fishros/fishbot-motion-control/docs/esp-drone/docs/_static/AFS_SEL.png

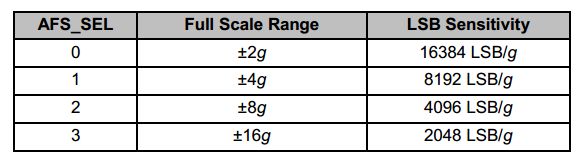
docs/esp-drone/docs/_static/AFS_SEL.png
