fishros/fishbot-motion-control/docs/esp-drone/docs/_static/api-reference.png

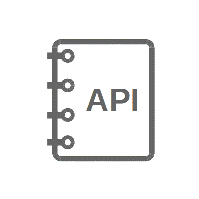
docs/esp-drone/docs/_static/api-reference.png
