fishros/fishbot-motion-control/docs/esp-drone/docs/_static/burst_read_sequence.png

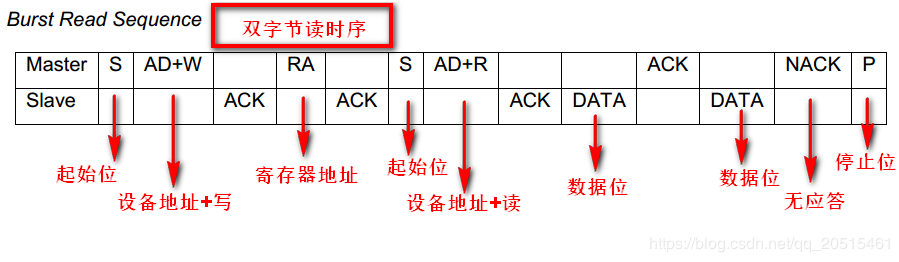
docs/esp-drone/docs/_static/burst_read_sequence.png
