fishros/fishbot-motion-control/docs/esp-drone/docs/_static/burst_write_sequence.png

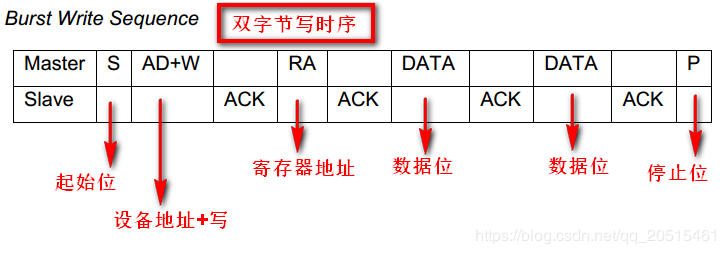
docs/esp-drone/docs/_static/burst_write_sequence.png
