fishros/fishbot-motion-control/docs/esp-drone/docs/_static/cover_page_pdf.jpg

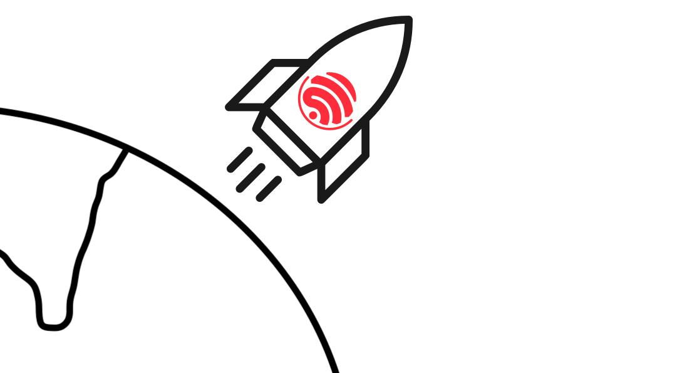
docs/esp-drone/docs/_static/cover_page_pdf.jpg
