fishros/fishbot-motion-control/docs/esp-drone/docs/_static/drivers_flie_struture.png

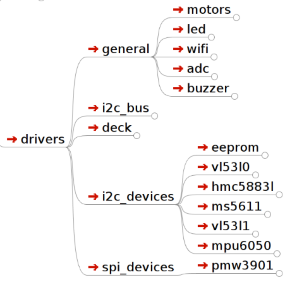
docs/esp-drone/docs/_static/drivers_flie_struture.png
