fishros/fishbot-motion-control/docs/esp-drone/docs/_static/espdrone_file_structure.png

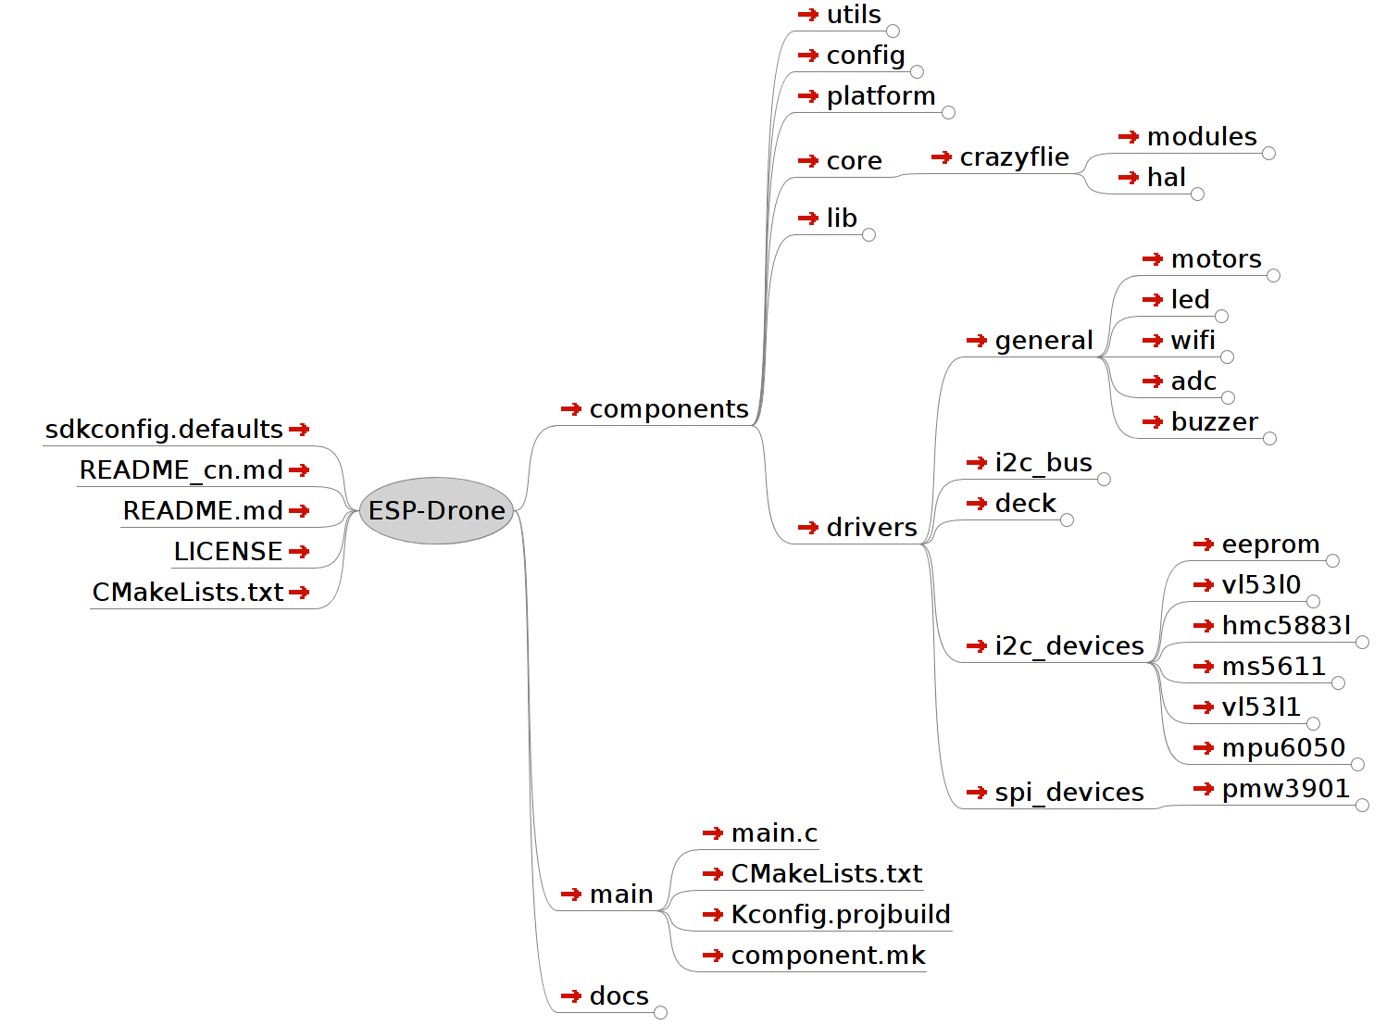
docs/esp-drone/docs/_static/espdrone_file_structure.png
