fishros/fishbot-motion-control/docs/esp-drone/docs/_static/espdrone_s2_v1_2_up2.jpg

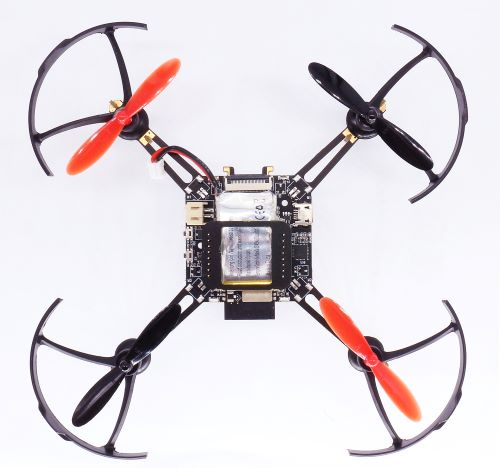
docs/esp-drone/docs/_static/espdrone_s2_v1_2_up2.jpg
