fishros/fishbot-motion-control/docs/esp-drone/docs/_static/espilot_app.png

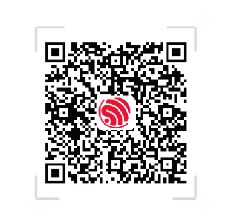
docs/esp-drone/docs/_static/espilot_app.png
