fishros/fishbot-motion-control/docs/esp-drone/docs/_static/esplane_2_0.jpg

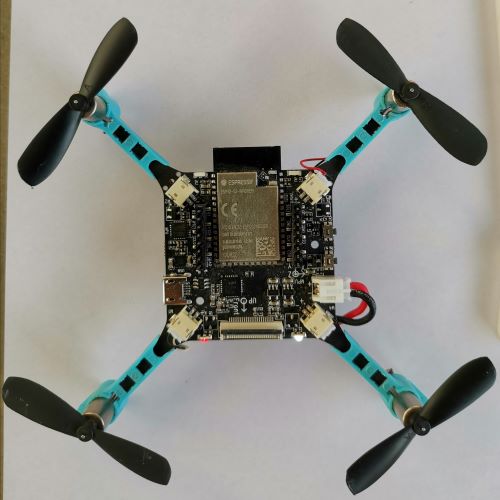
docs/esp-drone/docs/_static/esplane_2_0.jpg
