fishros/fishbot-motion-control/docs/esp-drone/docs/_static/FS_SEL.png

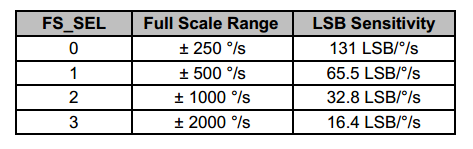
docs/esp-drone/docs/_static/FS_SEL.png
