fishros/fishbot-motion-control/docs/esp-drone/docs/_static/gamepad.jpg

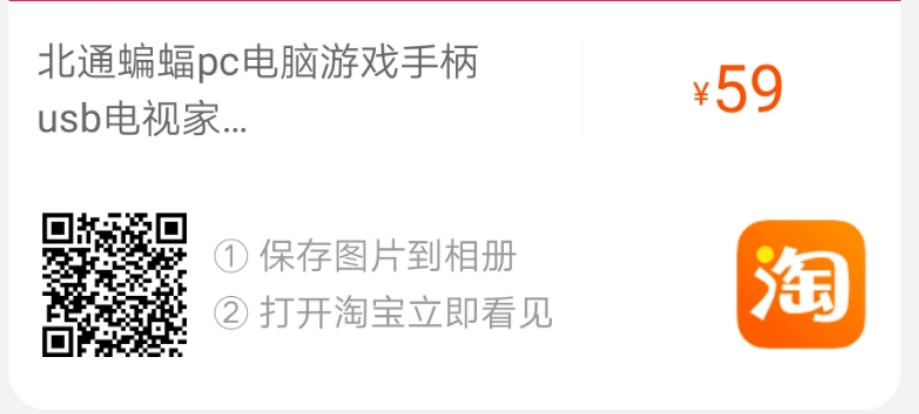
docs/esp-drone/docs/_static/gamepad.jpg
