fishros/fishbot-motion-control/docs/esp-drone/docs/_static/General-framework-of-the-stabilization-structure-of-the-crazyflie-with-setpoint-handling.png

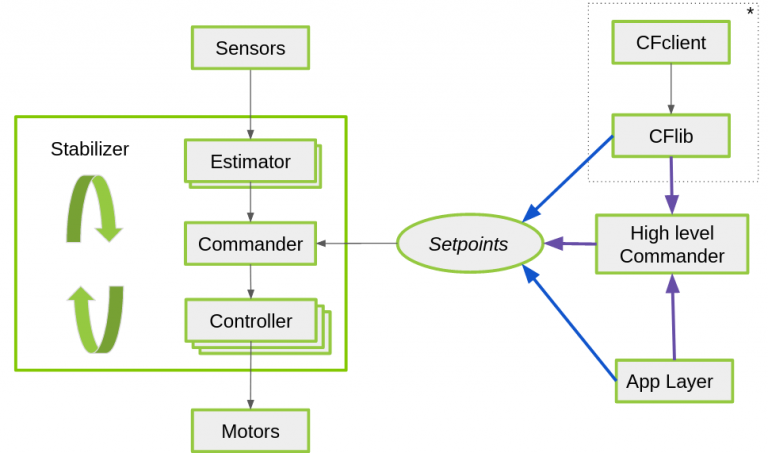
docs/esp-drone/docs/_static/General-framework-of-the-stabilization-structure-of-the-crazyflie-with-setpoint-handling.png
