fishros/fishbot-motion-control/docs/esp-drone/docs/_static/get-started.png

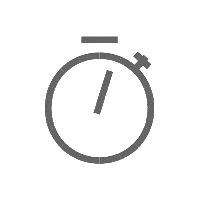
docs/esp-drone/docs/_static/get-started.png
