fishros/fishbot-motion-control/docs/esp-drone/docs/_static/hw-reference.png

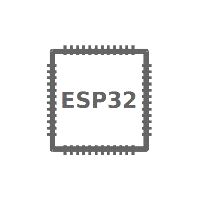
docs/esp-drone/docs/_static/hw-reference.png
