fishros/fishbot-motion-control/docs/esp-drone/docs/_static/log_motion.png

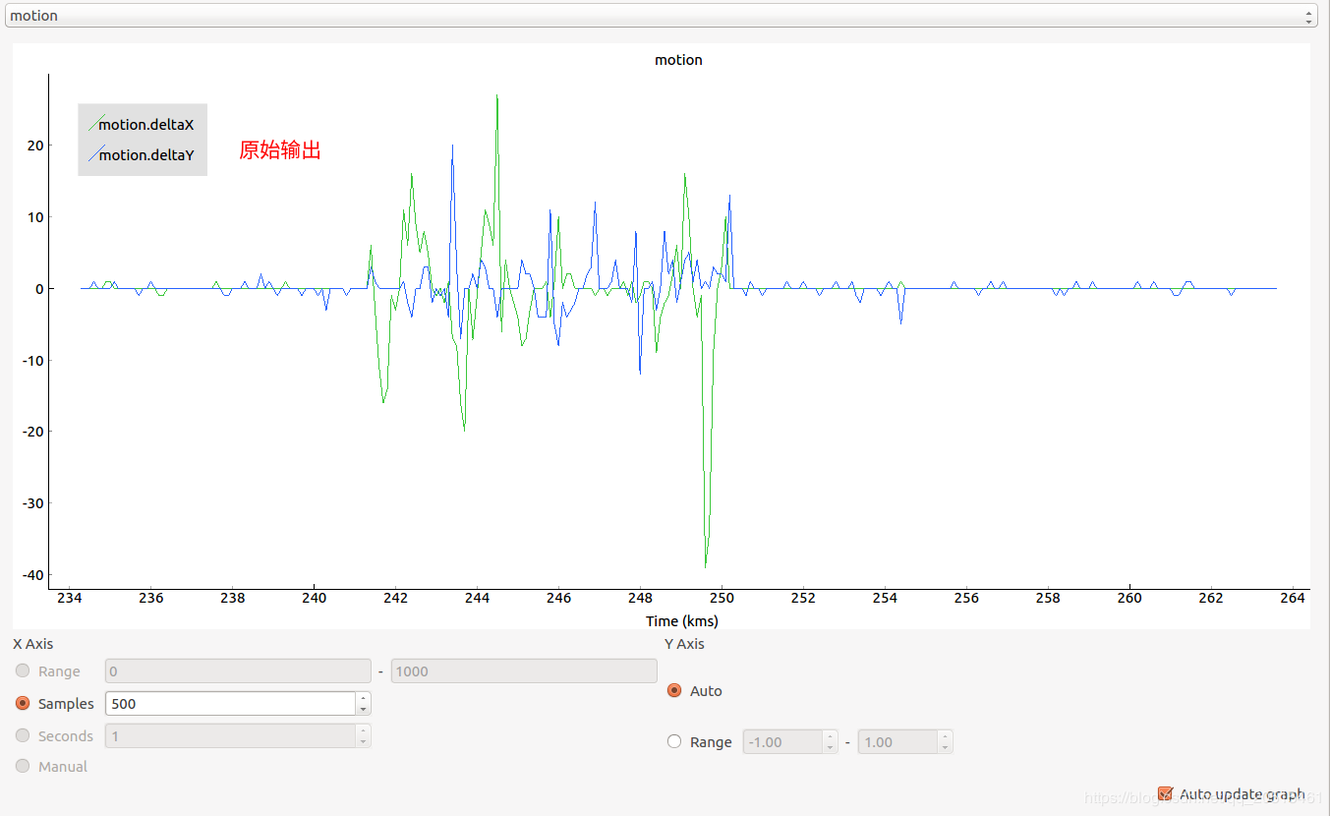
docs/esp-drone/docs/_static/log_motion.png
