fishros/fishbot-motion-control/docs/esp-drone/docs/_static/motors_direction.png

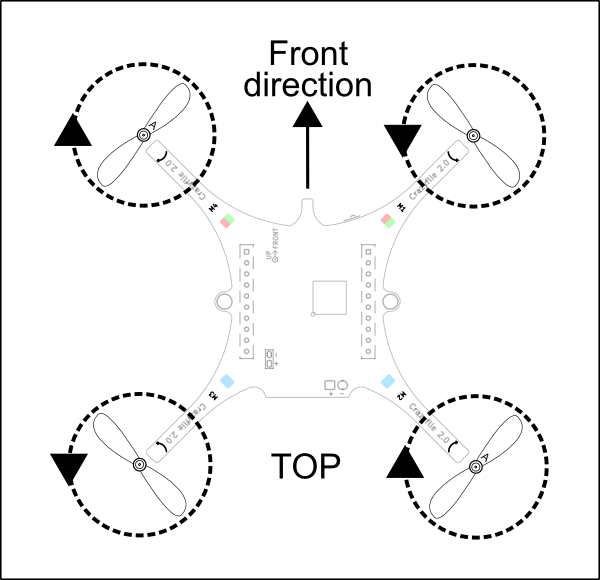
docs/esp-drone/docs/_static/motors_direction.png
