fishros/fishbot-motion-control/docs/esp-drone/docs/_static/mpu6050_dmp.png

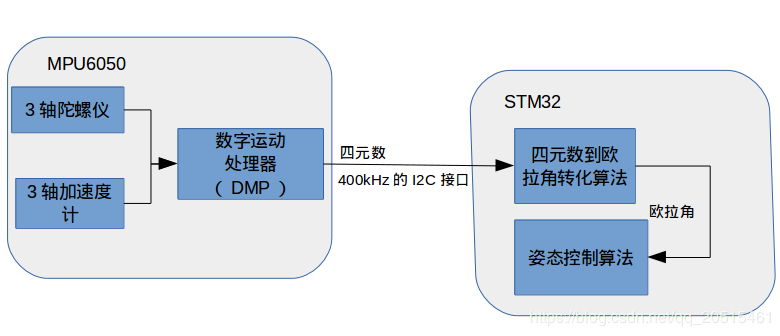
docs/esp-drone/docs/_static/mpu6050_dmp.png
