fishros/fishbot-motion-control/docs/esp-drone/docs/_static/mpu6050_dmp_en.png

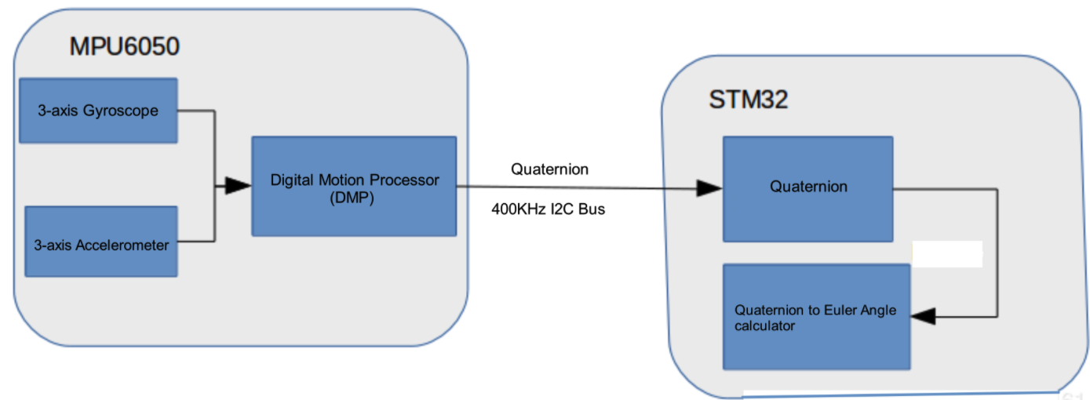
docs/esp-drone/docs/_static/mpu6050_dmp_en.png
