fishros/fishbot-motion-control/docs/esp-drone/docs/_static/mpu6050_int_plot.png

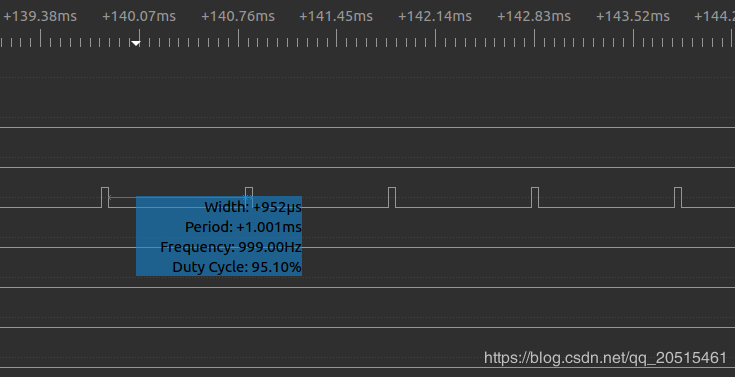
docs/esp-drone/docs/_static/mpu6050_int_plot.png
