fishros/fishbot-motion-control/docs/esp-drone/docs/_static/mpu6050_raw_value.png

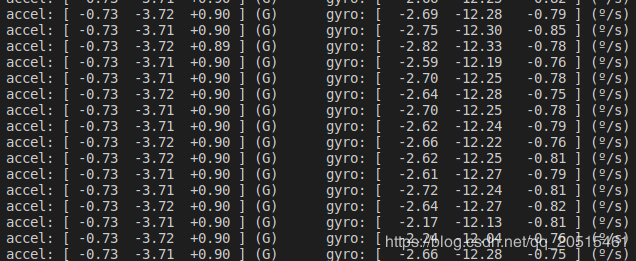
docs/esp-drone/docs/_static/mpu6050_raw_value.png
