fishros/fishbot-motion-control/docs/esp-drone/docs/_static/mpu6050_xyz.png

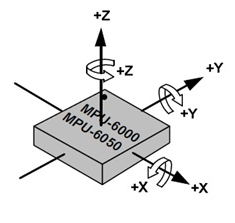
docs/esp-drone/docs/_static/mpu6050_xyz.png
