fishros/fishbot-motion-control/docs/esp-drone/docs/_static/network_settings.png

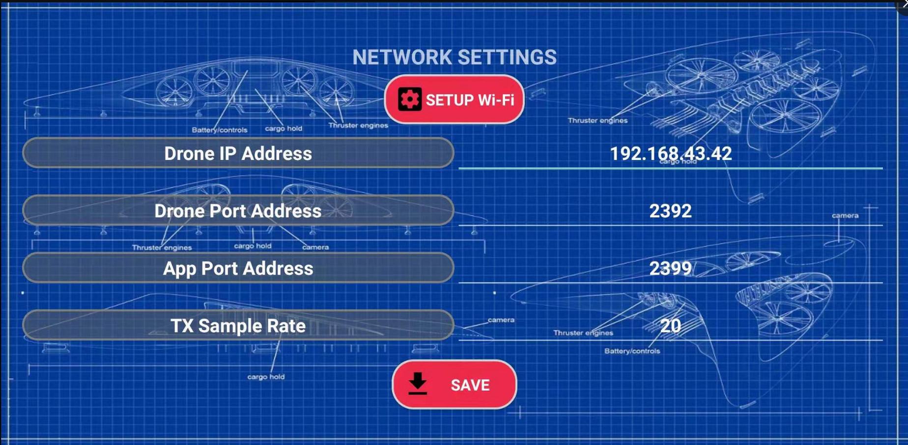
docs/esp-drone/docs/_static/network_settings.png
