fishros/fishbot-motion-control/docs/esp-drone/docs/_static/pmw3901_package.png

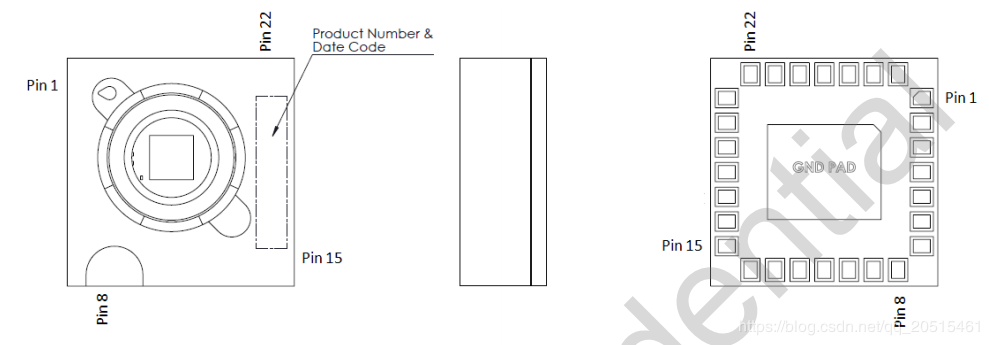
docs/esp-drone/docs/_static/pmw3901_package.png
