fishros/fishbot-motion-control/docs/esp-drone/docs/_static/pmw3901_pinmap.png

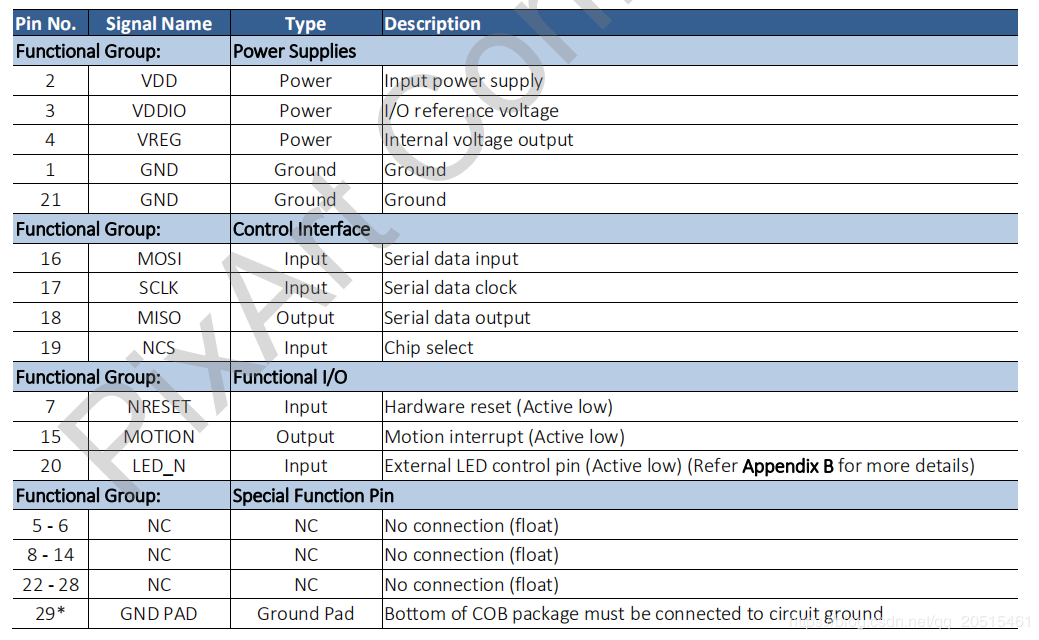
docs/esp-drone/docs/_static/pmw3901_pinmap.png
