fishros/fishbot-motion-control/docs/esp-drone/docs/_static/possible_controller_pathways.png

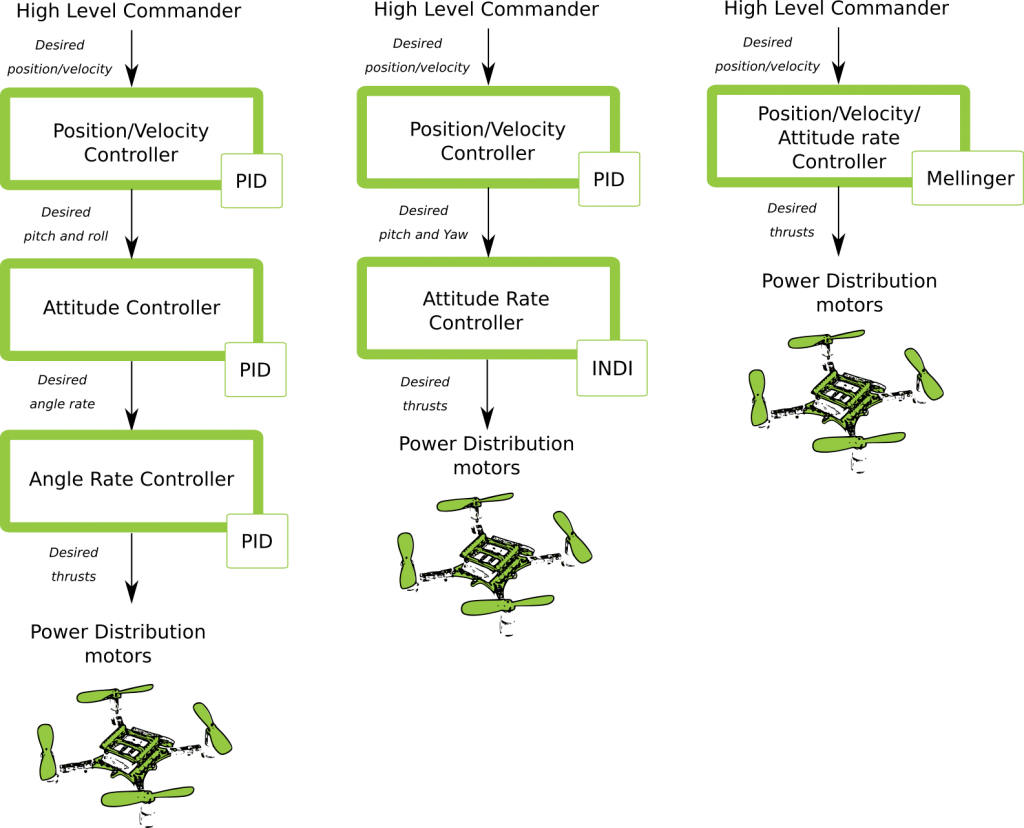
docs/esp-drone/docs/_static/possible_controller_pathways.png
