fishros/fishbot-motion-control/docs/esp-drone/docs/_static/REG_3B_40.png

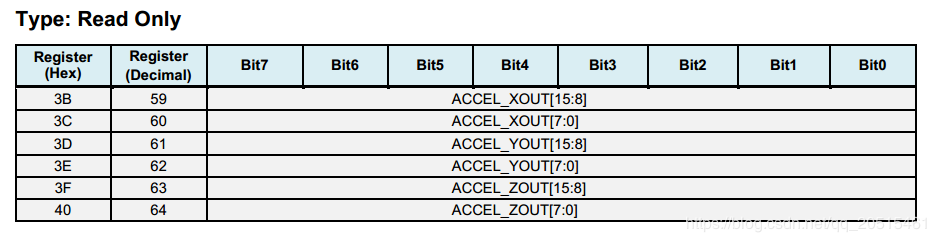
docs/esp-drone/docs/_static/REG_3B_40.png
