fishros/fishbot-motion-control/docs/esp-drone/docs/_static/REG_43_48.png

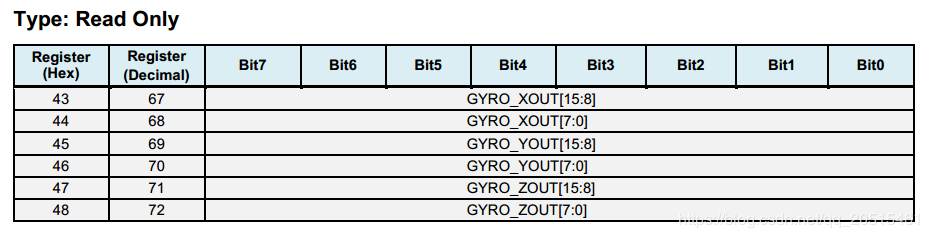
docs/esp-drone/docs/_static/REG_43_48.png
