fishros/fishbot-motion-control/docs/esp-drone/docs/_static/single_byte_read_sequence.png

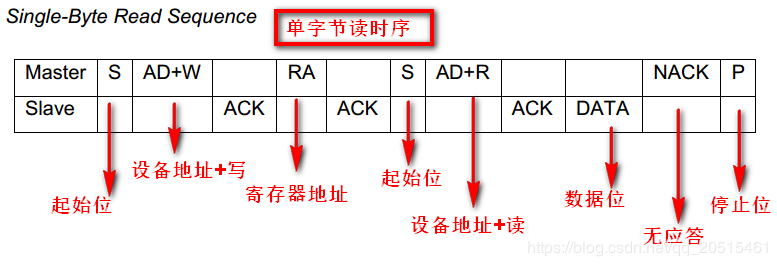
docs/esp-drone/docs/_static/single_byte_read_sequence.png
