fishros/fishbot-motion-control/docs/esp-drone/docs/_static/single_byte_WRITE_sequence.png

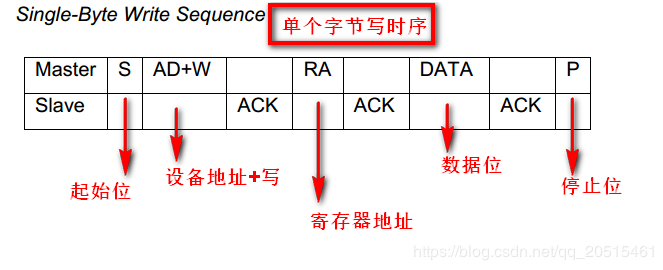
docs/esp-drone/docs/_static/single_byte_WRITE_sequence.png
