fishros/fishbot-motion-control/docs/esp-drone/docs/_static/stabilizerTask.png

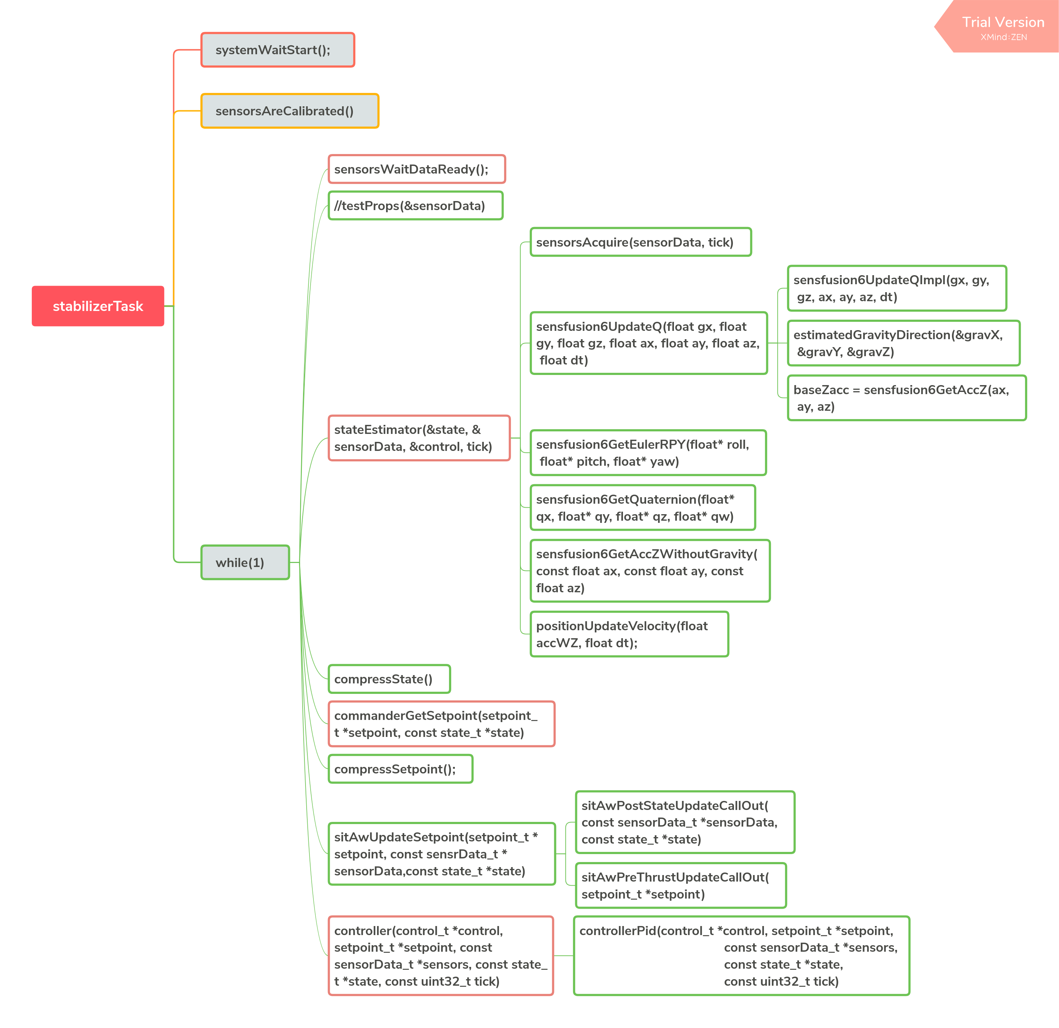
docs/esp-drone/docs/_static/stabilizerTask.png
