fishros/fishbot-motion-control/docs/esp-drone/docs/_static/stabilizerTask_process.png

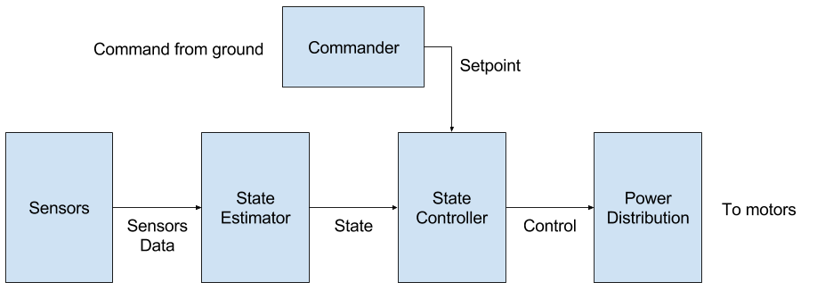
docs/esp-drone/docs/_static/stabilizerTask_process.png
