fishros/fishbot-motion-control/docs/esp-drone/docs/_static/start_from_app_main.png

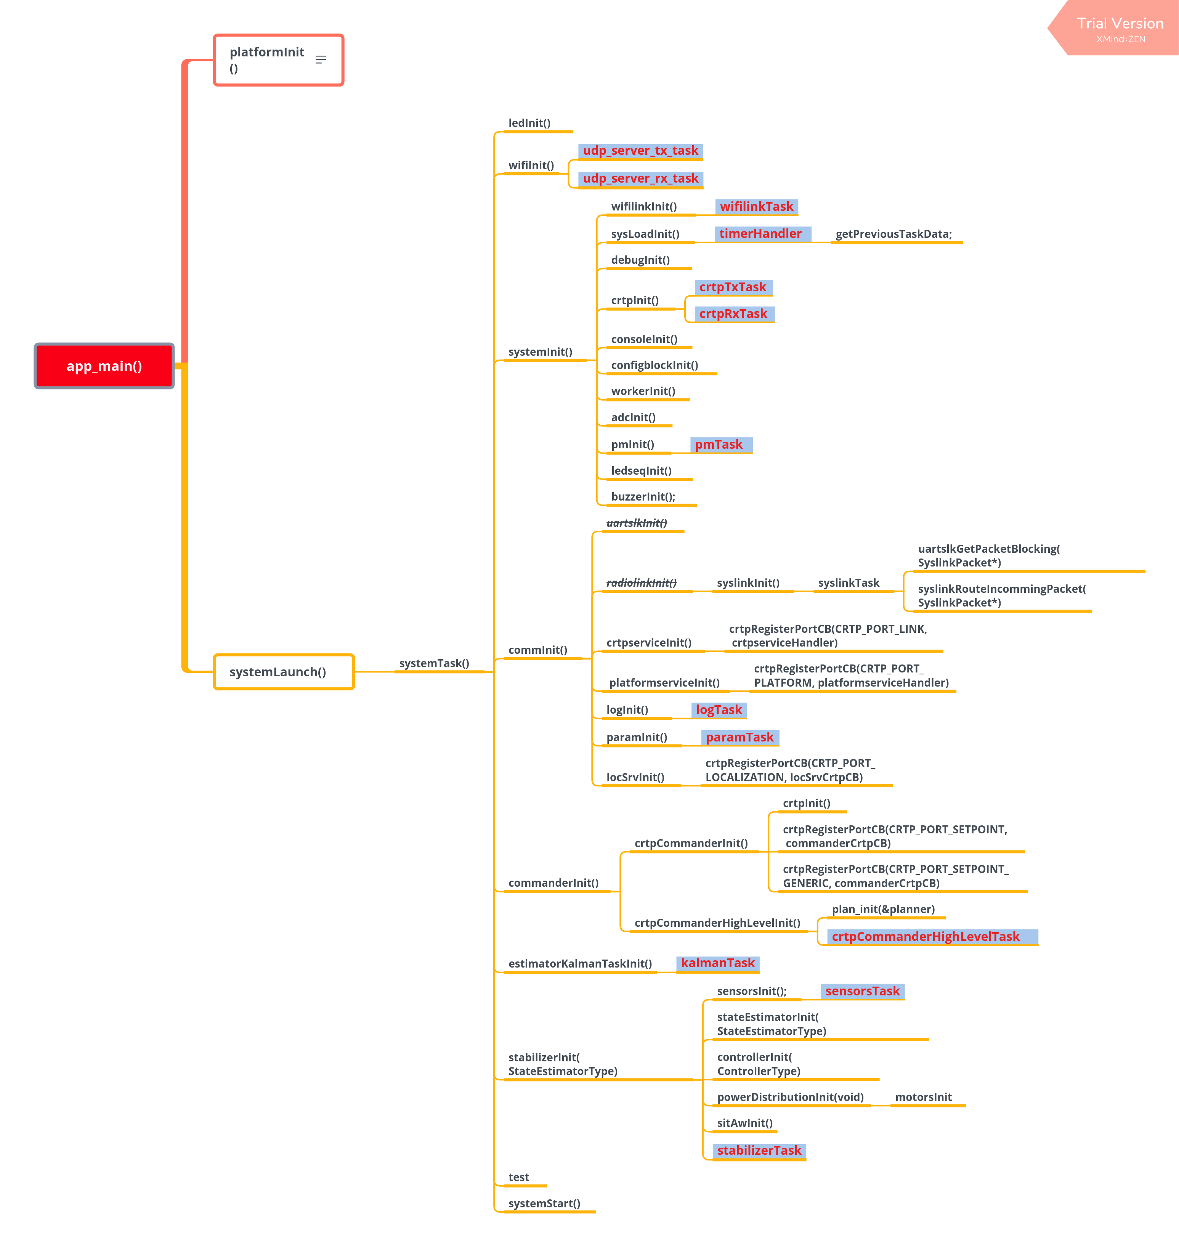
docs/esp-drone/docs/_static/start_from_app_main.png
