fishros/fishbot-motion-control/docs/esp-drone/docs/_static/task_dump.png

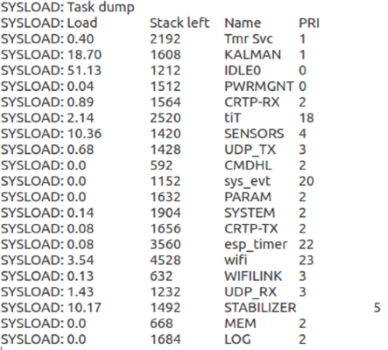
docs/esp-drone/docs/_static/task_dump.png
