fishros/fishbot-motion-control/docs/esp-drone/docs/_static/vl53l1x_api_platform.png

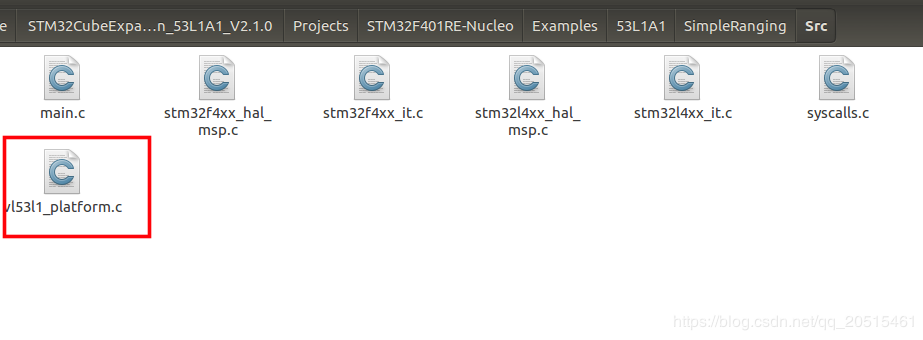
docs/esp-drone/docs/_static/vl53l1x_api_platform.png
