fishros/fishbot-motion-control/docs/esp-drone/docs/_static/vl53l1x_package.png

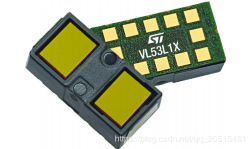
docs/esp-drone/docs/_static/vl53l1x_package.png
