fishros/fishbot-motion-control/docs/esp-drone/docs/_static/vl53lxx_api_platform.png

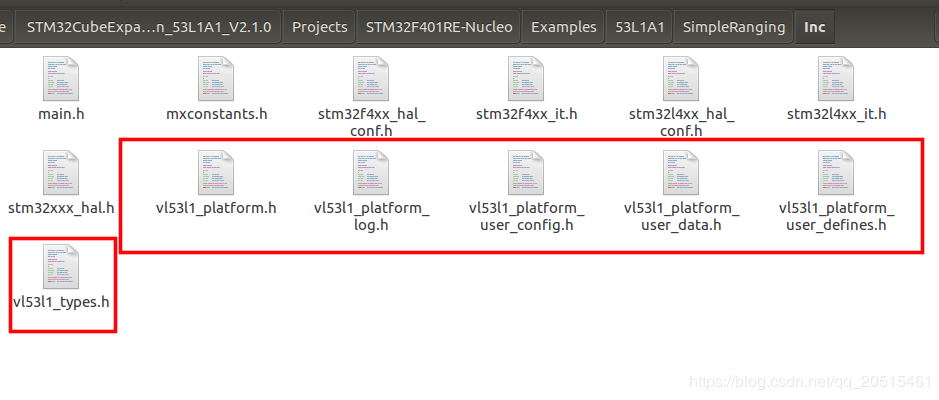
docs/esp-drone/docs/_static/vl53lxx_api_platform.png
