fishros/fishbot-motion-control/docs/esp-drone/docs/_static/vl53lxx_mode.png

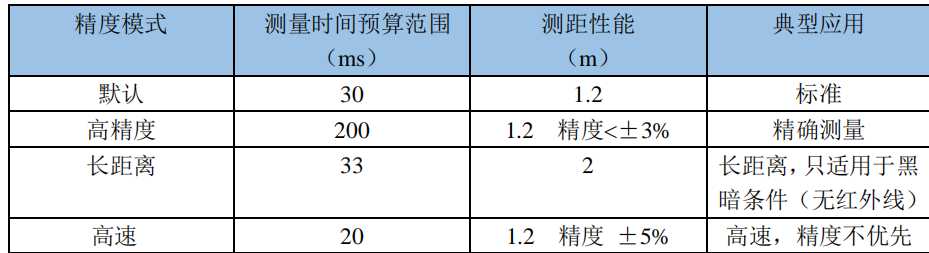
docs/esp-drone/docs/_static/vl53lxx_mode.png
