fishros/fishbot-motion-control/docs/esp-drone/docs/_static/vl53lxx_roi.png

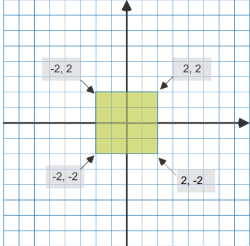
docs/esp-drone/docs/_static/vl53lxx_roi.png
