fishros/fishbot-motion-control/docs/esp-drone/docs/_static/vl53lxx_roi_2.png

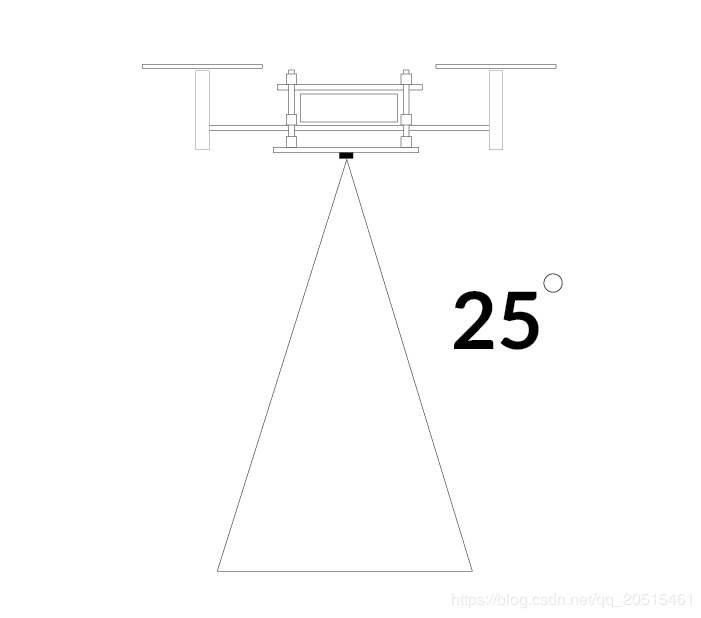
docs/esp-drone/docs/_static/vl53lxx_roi_2.png
