fishros/fishbot-motion-control/docs/esp-drone/docs/_static/vl53lxx_calibrate_gui.png

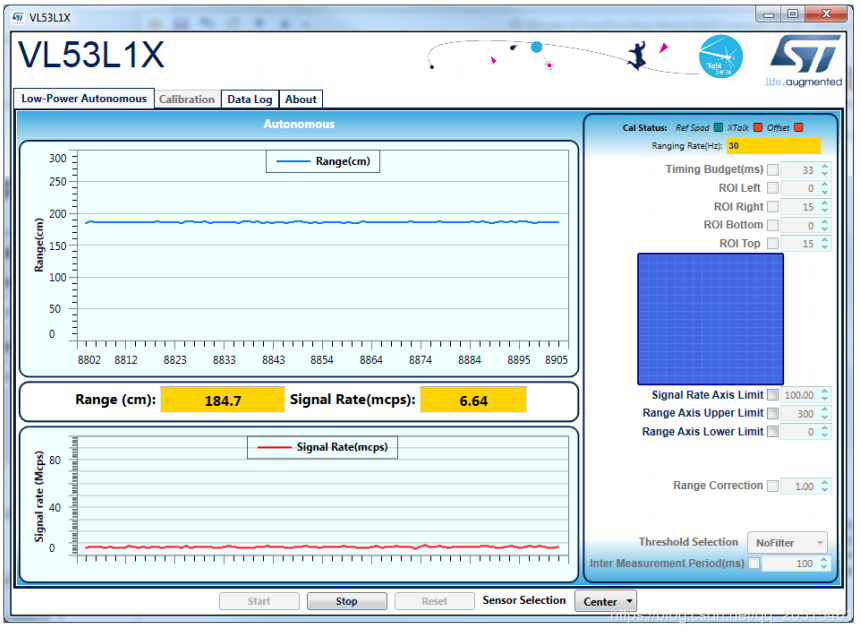
docs/esp-drone/docs/_static/vl53lxx_calibrate_gui.png
