fishros/fishbot-motion-control/docs/esp-drone/docs/_static/vl53lxx_calibration_sequence.png

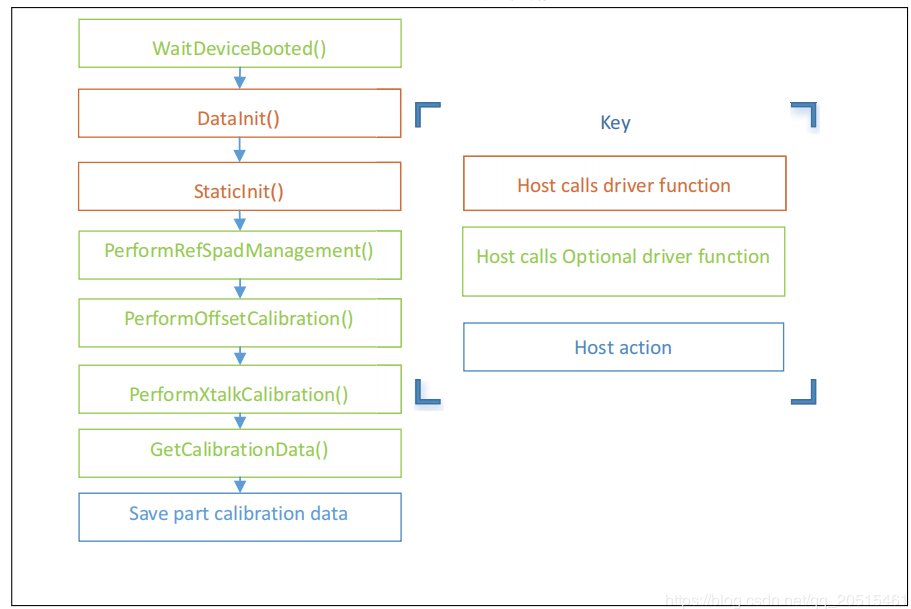
docs/esp-drone/docs/_static/vl53lxx_calibration_sequence.png
